shunakiyama/fridge-temp-monitor/pics/plans.png

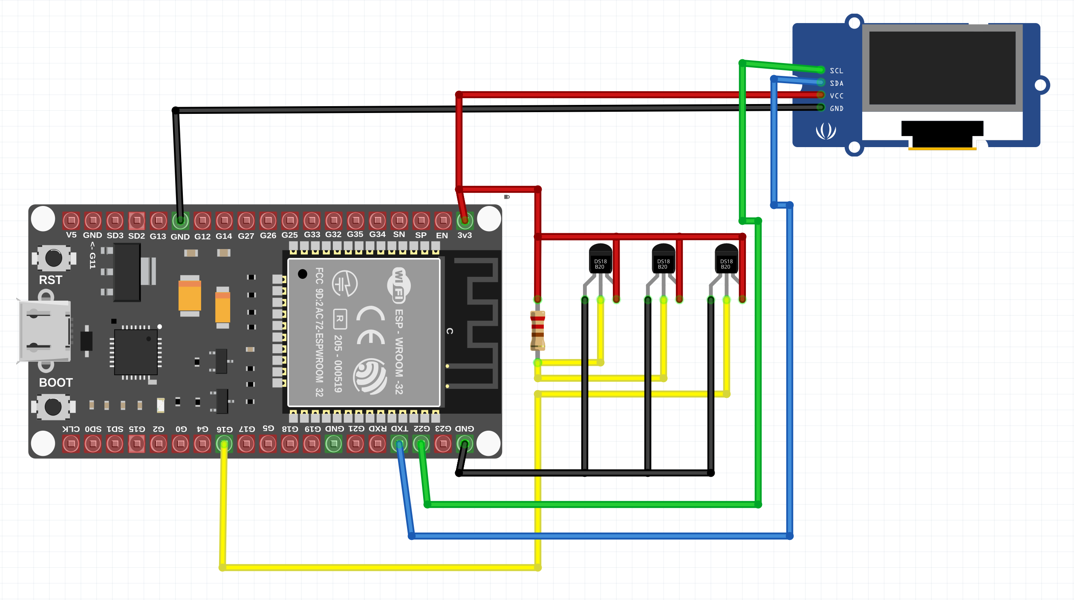
pics/plans.png
